hsgw/lain/img/alpha/lain-2.jpg

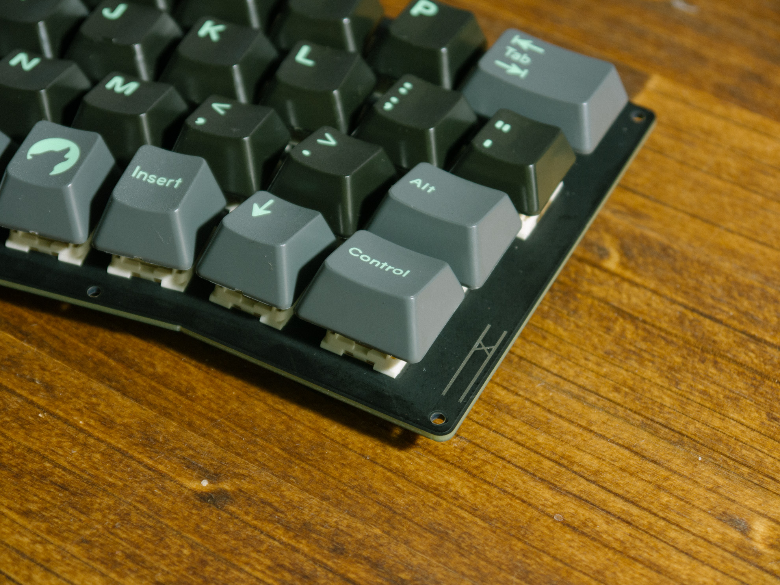
img/alpha/lain-2.jpg
