hsgw/lain/img/alpha/lain_bottom.jpg

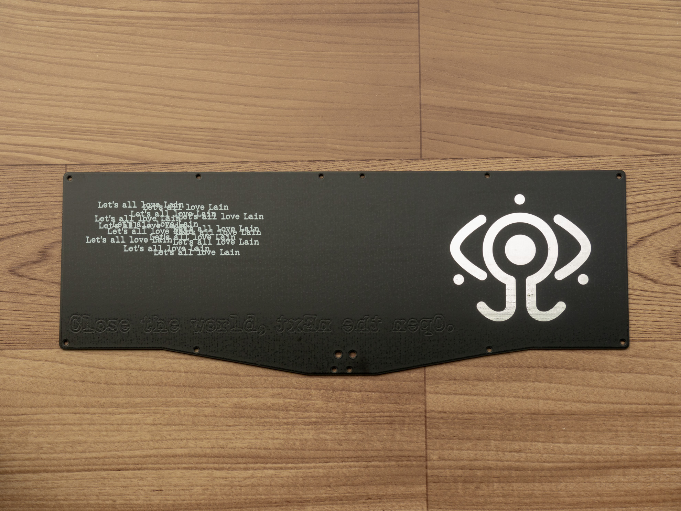
img/alpha/lain_bottom.jpg
