hsgw/lain/img/alpha/lain_pcb.jpg

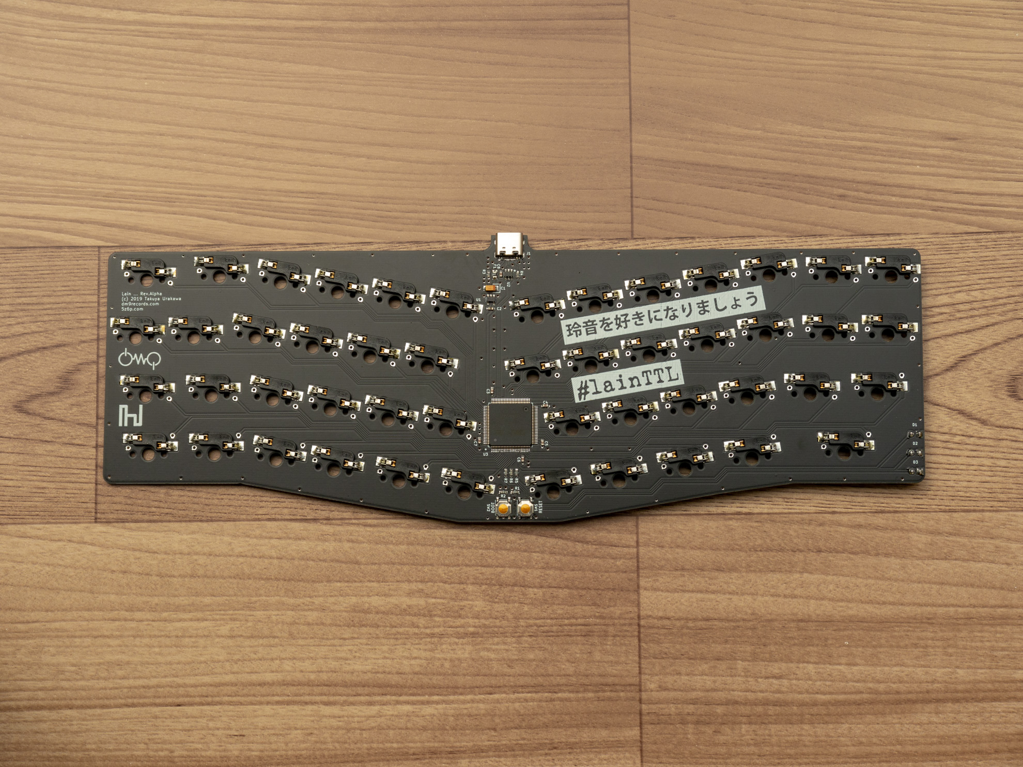
img/alpha/lain_pcb.jpg
